dmsmccann/Spectrum-Analyzer/images/70mhz-lp-50mhz-to-100mhz.png

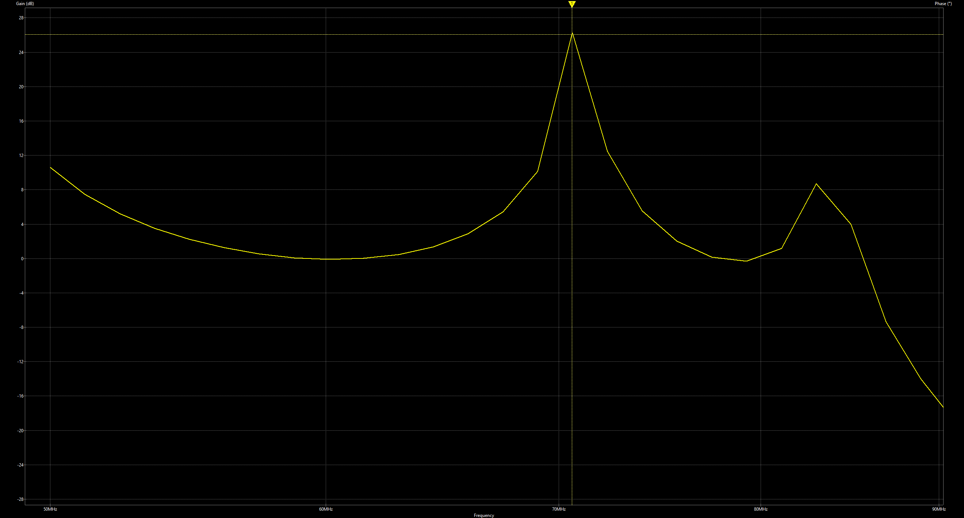
images/70mhz-lp-50mhz-to-100mhz.png
