dmsmccann/Spectrum-Analyzer/resolution-filters/resolution-filters/crystal-filter-nanovna-h4_2023-01-16_13-13-07.png

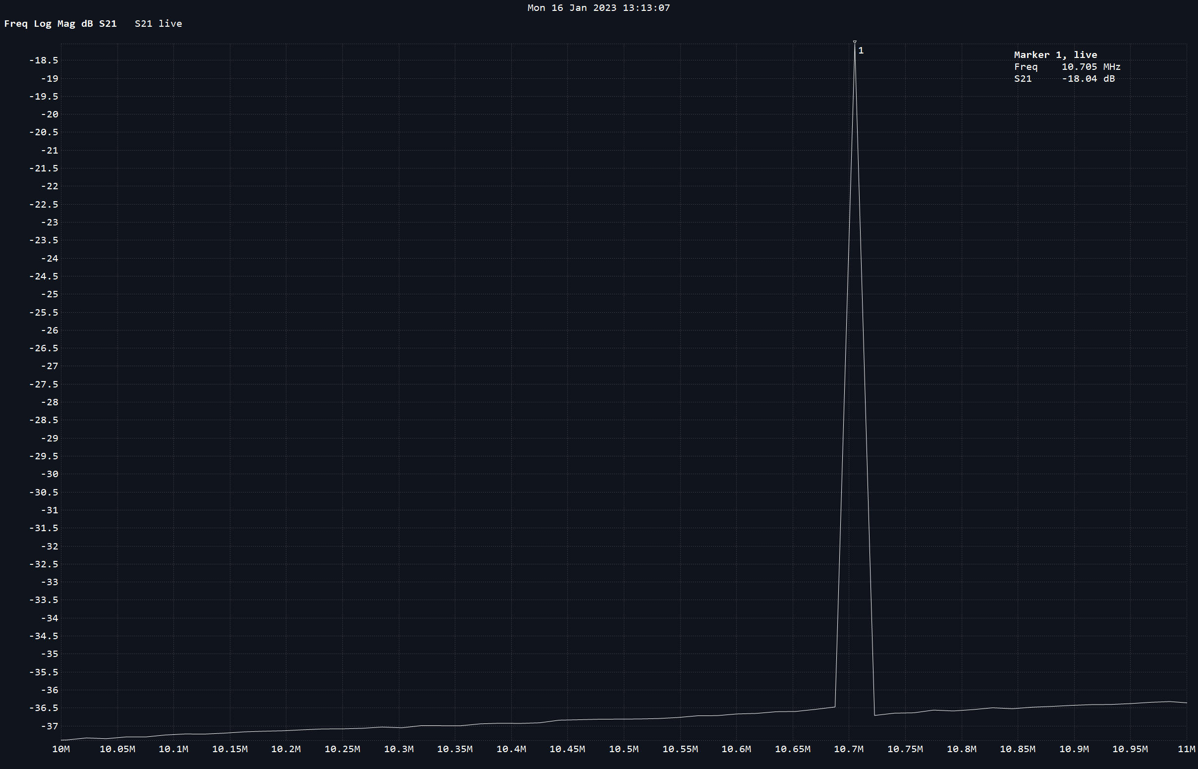
resolution-filters/resolution-filters/crystal-filter-nanovna-h4_2023-01-16_13-13-07.png
