dmsmccann/Spectrum-Analyzer/resolution-filters/resolution-filters/l501-smith-chart.png

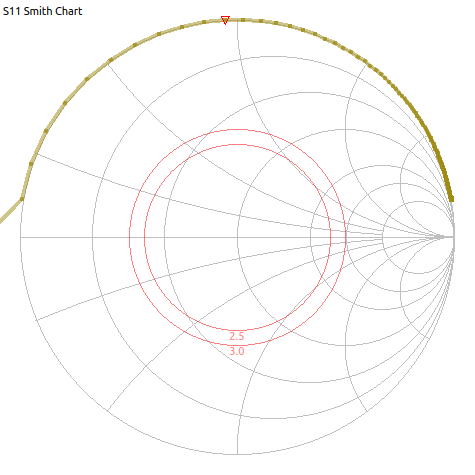
resolution-filters/resolution-filters/l501-smith-chart.png
