dmsmccann/Spectrum-Analyzer/Screenshot 2022-08-23 135709.gif

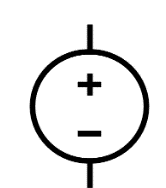
Screenshot 2022-08-23 135709.gif
