dmsmccann/Spectrum-Analyzer/tracking-generator/Screenshot 2023-12-05 054804.png

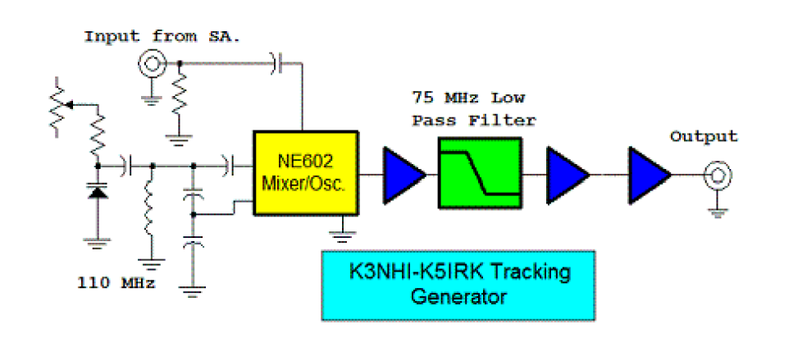
tracking-generator/Screenshot 2023-12-05 054804.png
