dmsmccann/Spectrum-Analyzer/if-and-log-amp/if-and-log-amp/if-log-amp-models/if-log-amp-3D/terminal-block.FCStd

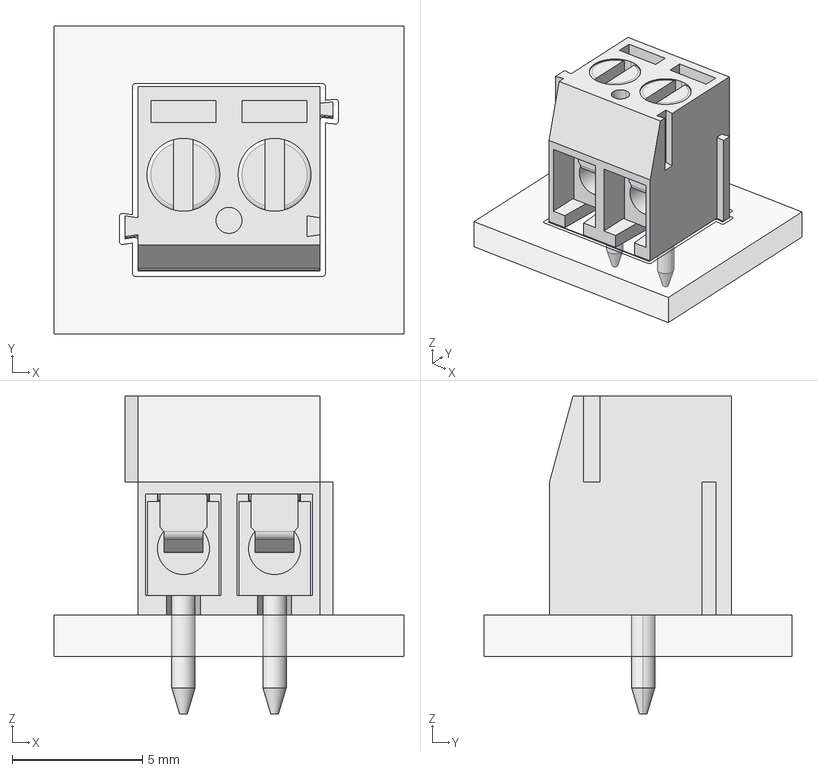
[picture p33: CAD file, 2022-08-05]
if-and-log-amp/if-and-log-amp/if-log-amp-models/if-log-amp-3D/terminal-block.FCStd
13.4 x 11.8 x 12.2 mm
FFab
FrontSilk
TopPads
BotPads
PTHs
Pcb
