dmsmccann/Spectrum-Analyzer/resolution-filters/resolution-filters/resolution-filters-models/resolution-filters-3D/UM-007.step

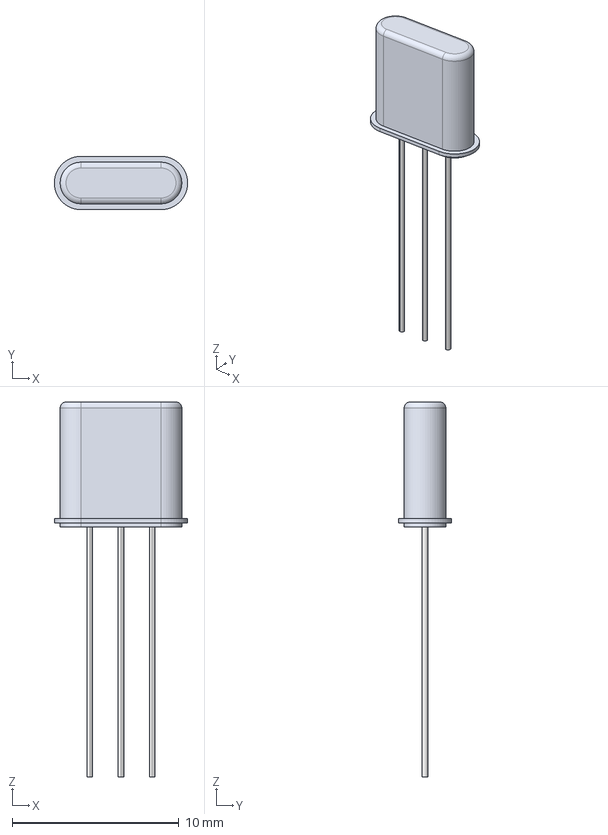
[picture p34: CAD file, 2022-08-05]
resolution-filters/resolution-filters/resolution-filters-models/resolution-filters-3D/UM-007.step
8.00 x 3.20 x 22.5 mm
UM-1
UM-002
UM-003
UM-004
UM-005
UM-006
