dmsmccann/Spectrum-Analyzer/15v-supply/15v-supply-models/15v-supply-3D/CAP_QYX_3P5X6X8P5_NCH.step

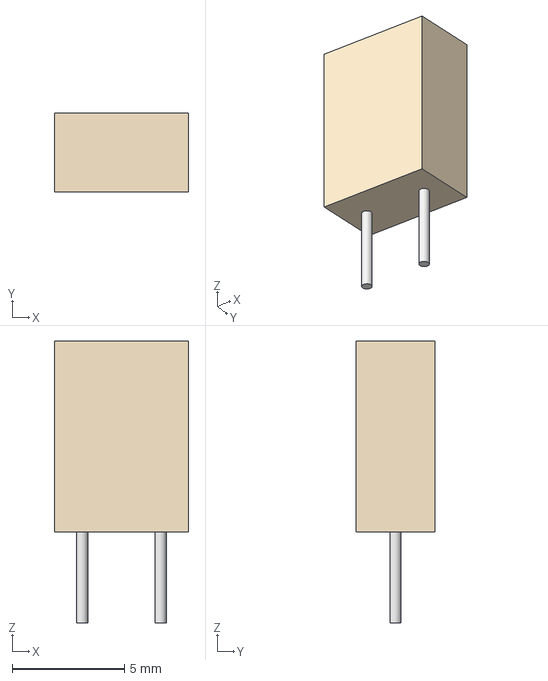
[picture p35: CAD file, 2022-06-16]
15v-supply/15v-supply-models/15v-supply-3D/CAP_QYX_3P5X6X8P5_NCH.step
5.99 x 3.51 x 12.6 mm
