dmsmccann/Spectrum-Analyzer/hierarchical-schematic/spectrum-analyzer-models/hammond-enclosure.FCStd

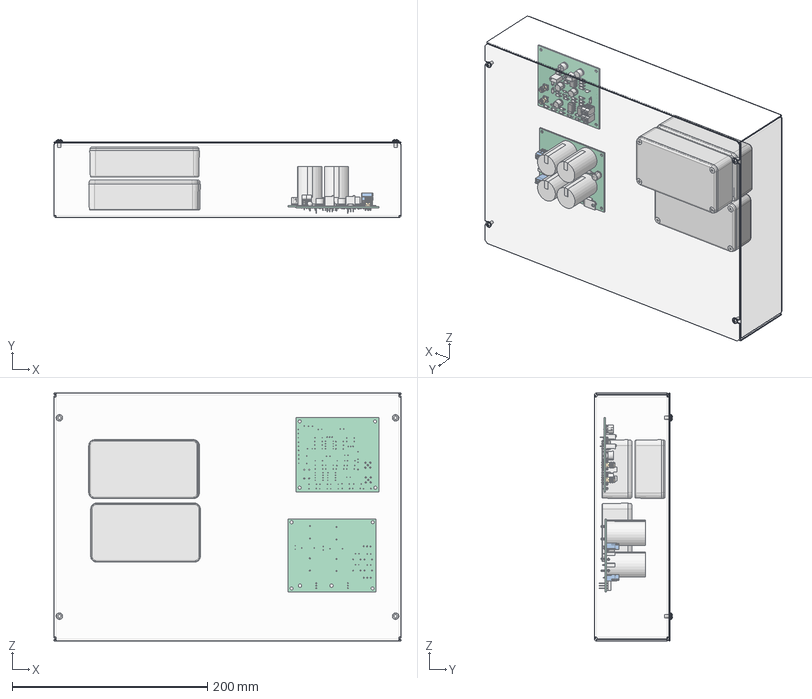
[picture p36: CAD file, 2023-04-26]
hierarchical-schematic/spectrum-analyzer-models/hammond-enclosure.FCStd
355.6 x 80.0 x 254.0 mm
1590B BOX
1590B-BS LID
SC530 (screw #6-32X 1_2' FH)
SC530 (screw #6-32X 1_2' FH)001
SC530 (screw #6-32X 1_2' FH)002
SC530 (screw #6-32X 1_2' FH)003
1590B BOX001
1590B-BS LID001
SC530 (screw #6-32X 1_2' FH)004
SC530 (screw #6-32X 1_2' FH)005
SC530 (screw #6-32X 1_2' FH)006
SC530 (screw #6-32X 1_2' FH)007
1590B BOX002
1590B-BS LID002
SC530 (screw #6-32X 1_2' FH)008
SC530 (screw #6-32X 1_2' FH)009
SC530 (screw #6-32X 1_2' FH)010
SC530 (screw #6-32X 1_2' FH)011
Pcb_7b02
D901_D_DO-41_SOD81_P7.62mm_Horizontal_0f7420698e15 x 4
R902_R_Axial_DIN0309_L90mm_D32mm_P1270mm_Horizontal_656395d6a1e4 x 2
C904_CP_Radial_D80mm_P350mm_be9362f17a2f x 2
U902_TO-220-3_Horizontal_TabUp_336c31f2f8c4 x 4
Pcb_758f
R426_R_Axial_DIN0207_L63mm_D25mm_P762mm_Horizontal_96b38c16849e x 27
D_DO-35_SOD27_P7.62mm_Horizontal x 7
D_DO-35_SOD27_P7.62mm_Horizontal001 x 7
C405_CP_Radial_D80mm_P350mm_98bf3544fc31 x 5
C401_C_Disc_D50mm_W25mm_P500mm_d1dd1edc5a97
OPA347PA x 3
OPA347PA001 x 3
OPA347PA002 x 3
OPA347PA003 x 3
OPA347PA004 x 3
OPA347PA005 x 3
OPA347PA006 x 3
OPA347PA007 x 3
OPA347PA008 x 3
OPA347PA009 x 3
R424_Potentiometer_Bourns_3296W_Vertical_5014a80db3f9 x 2
6-32 (SC18394)004
6-32 (SC18394)005
6-32 (SC18394)006
6-32 (SC18394)007
