dmsmccann/Spectrum-Analyzer/if-and-log-amp/if-and-log-amp/if-log-amp-models/if-log-amp-3D/ad8307.step

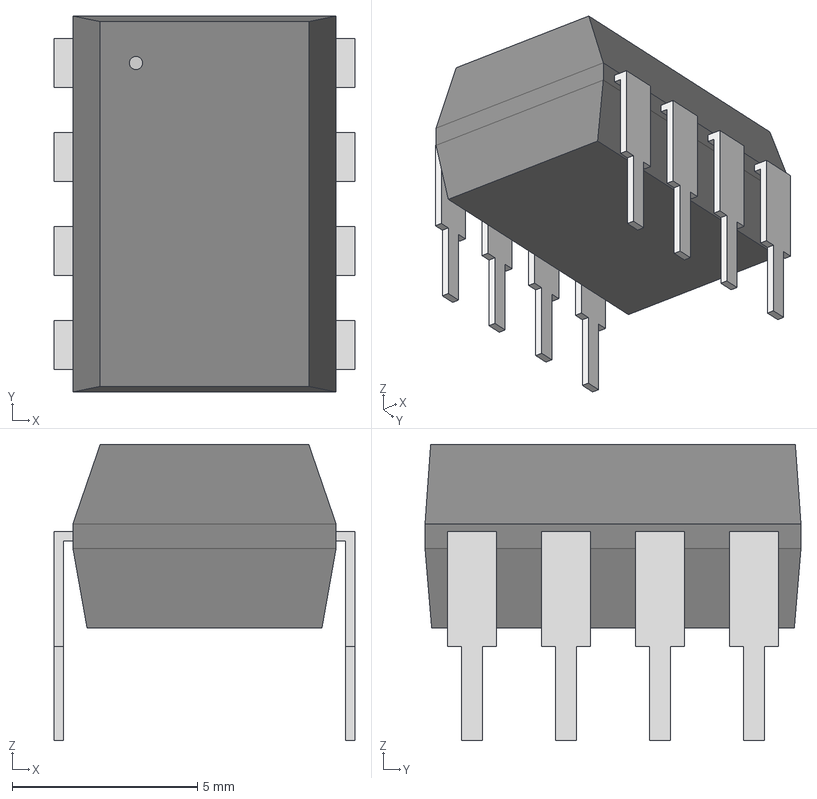
[picture p37: CAD file, 2022-08-05]
if-and-log-amp/if-and-log-amp/if-log-amp-models/if-log-amp-3D/ad8307.step
8.13 x 10.2 x 8.00 mm
