dmsmccann/Spectrum-Analyzer/15v-supply/15v-supply-models/15v-supply-3D/terminal-block-691103110003.step

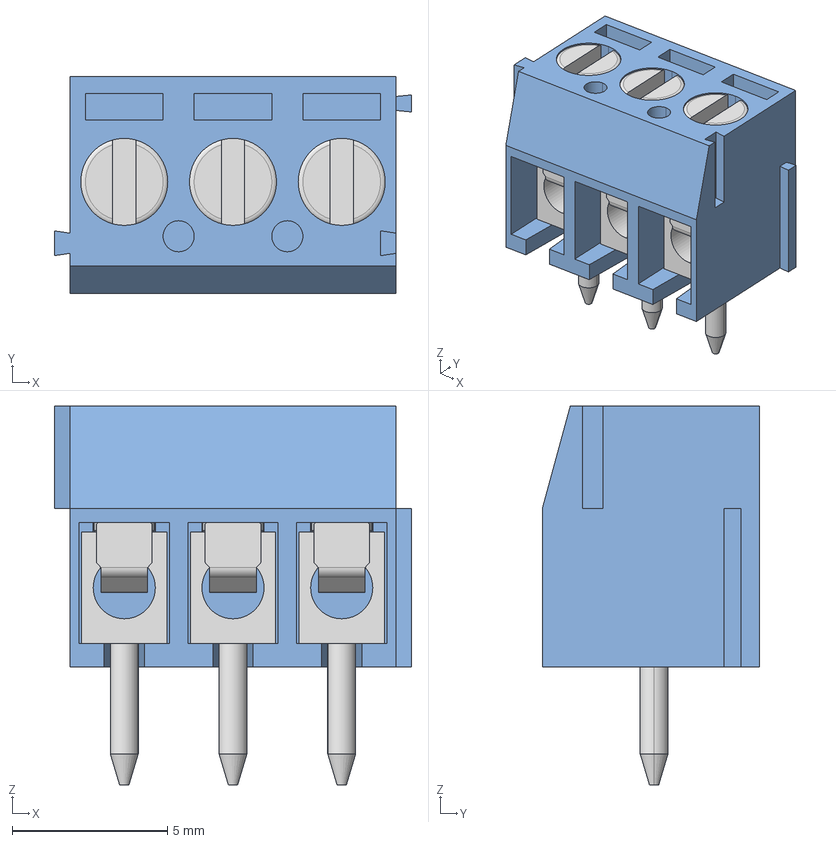
[picture p38: CAD file, 2022-06-16]
15v-supply/15v-supply-models/15v-supply-3D/terminal-block-691103110003.step
11.5 x 7.00 x 12.2 mm
