dmsmccann/Spectrum-Analyzer/hierarchical-schematic/spectrum-analyzer-models/1444-14103.stp

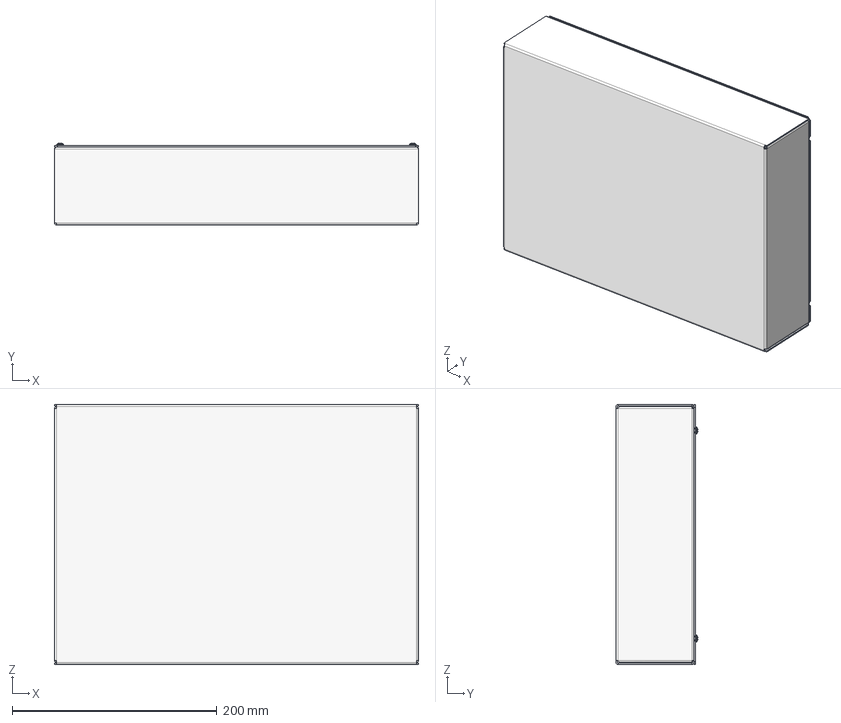
[picture p39: CAD file, 2023-04-26]
hierarchical-schematic/spectrum-analyzer-models/1444-14103.stp
355.6 x 80.0 x 254.0 mm
6-32 (SC18394) x 4
