dmsmccann/Spectrum-Analyzer/if-and-log-amp/if-and-log-amp/if-log-amp-models/if-log-amp-3D/toroid.FCStd

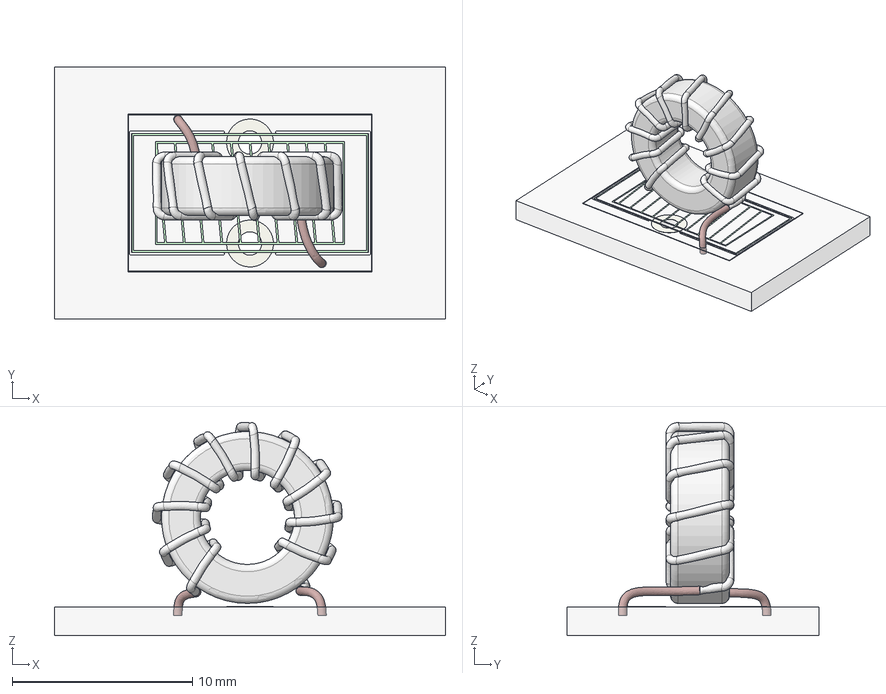
[picture p40: CAD file, 2022-08-05]
if-and-log-amp/if-and-log-amp/if-log-amp-models/if-log-amp-3D/toroid.FCStd
21.7 x 14.0 x 11.8 mm
FCrtYd
FFab
FrontSilk
TopPads
BotPads
PTHs
Pcb
T37-6 IND
T37-6 IND001
T37-6 IND002
T37-6 IND003
