dmsmccann/Spectrum-Analyzer/resolution-filters/resolution-filters/resolution-filters-models/resolution-filters-3D/T37-6 IND.STEP

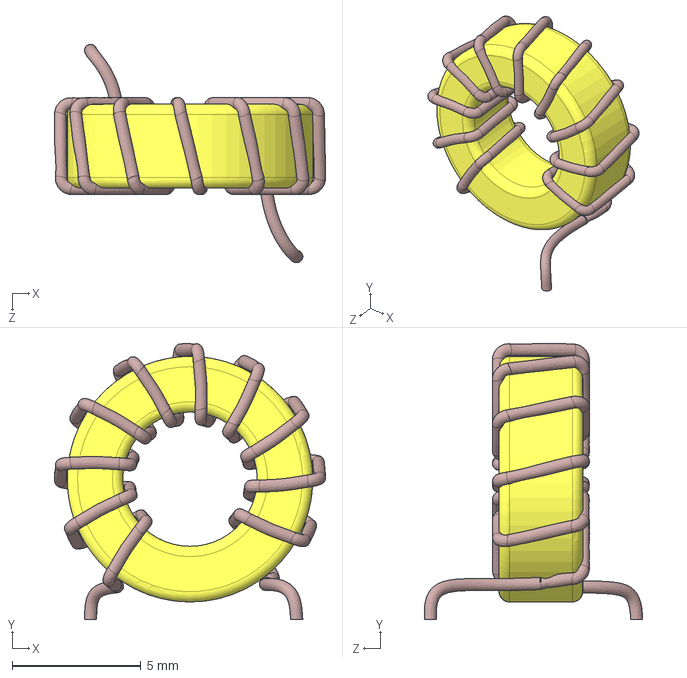
[picture p41: CAD file, 2022-08-05]
resolution-filters/resolution-filters/resolution-filters-models/resolution-filters-3D/T37-6 IND.STEP
10.5 x 10.7 x 8.47 mm
