dmsmccann/Spectrum-Analyzer/timebase/timebase/timebase-models/timebase-3D/NL17SZ74USG.step

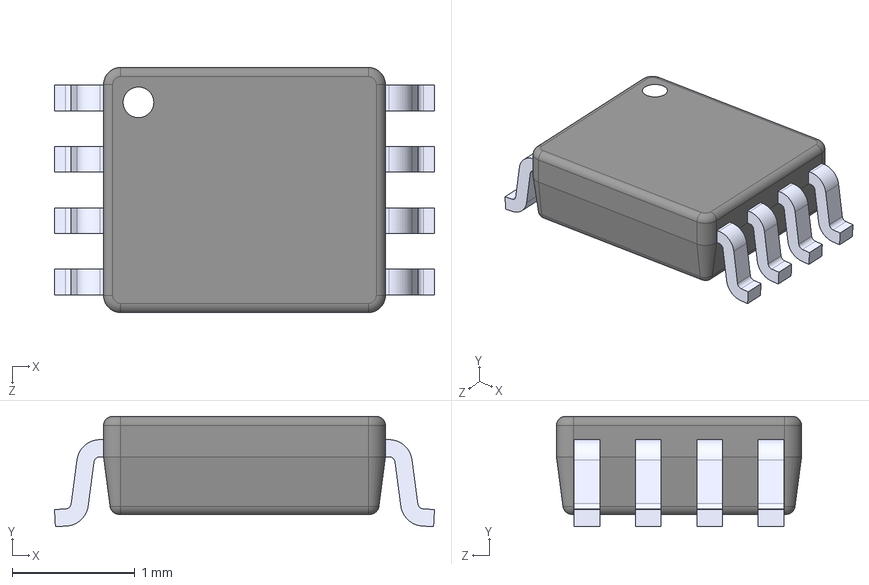
[picture p42: CAD file, 2022-06-18]
timebase/timebase/timebase-models/timebase-3D/NL17SZ74USG.step
3.10 x 0.9 x 2.00 mm
