dmsmccann/Spectrum-Analyzer/hierarchical-schematic/spectrum-analyzer-models/1590B.stp

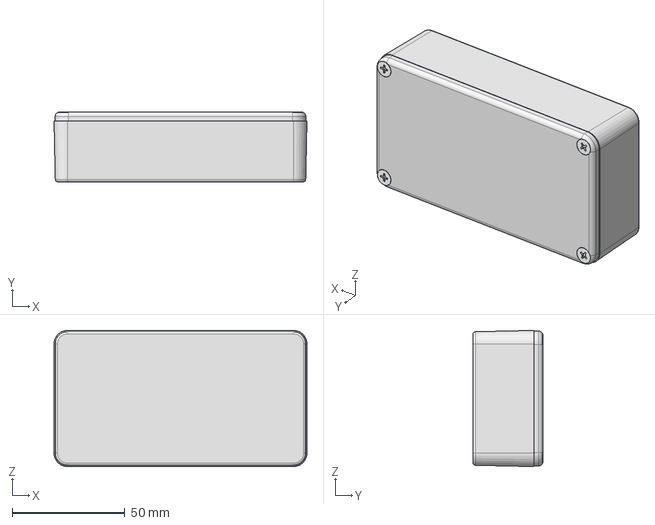
[picture p43: CAD file, 2022-06-01]
hierarchical-schematic/spectrum-analyzer-models/1590B.stp
112.4 x 31.0 x 60.5 mm
