dmsmccann/Spectrum-Analyzer/if-and-log-amp/if-and-log-amp/if-log-amp-models/if-log-amp-3D/Bourns 3386G.FCStd

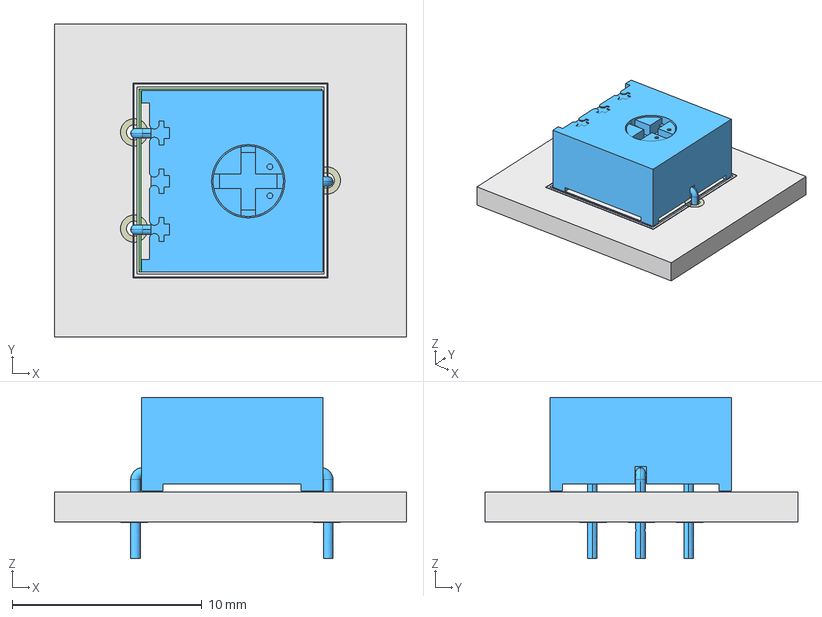
[picture p44: CAD file, 2022-08-05]
if-and-log-amp/if-and-log-amp/if-log-amp-models/if-log-amp-3D/Bourns 3386G.FCStd
18.6 x 16.5 x 8.51 mm
FCrtYd
FFab
FrontSilk
TopPads
BotPads
PTHs
Pcb
