dmsmccann/Spectrum-Analyzer/resolution-filters/resolution-filters/resolution-filters-models/resolution-filters-3D/L_Tor_13x8x5_3a.stp

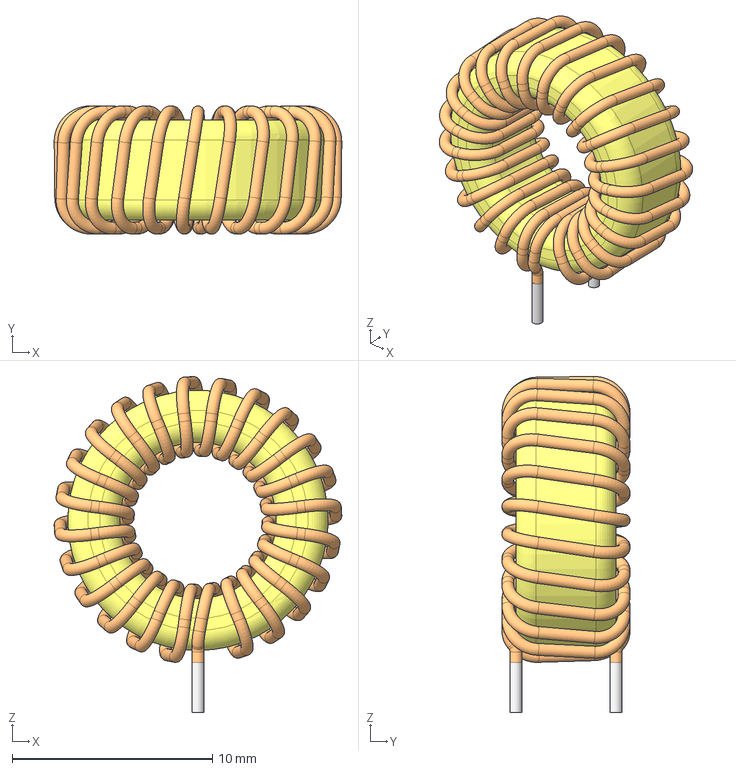
[picture p45: CAD file, 2022-08-05]
resolution-filters/resolution-filters/resolution-filters-models/resolution-filters-3D/L_Tor_13x8x5_3a.stp
14.4 x 6.40 x 16.8 mm
