dmsmccann/Spectrum-Analyzer/timebase/timebase/timebase-models/timebase-3D/CUI_Devices_PJ_009.step

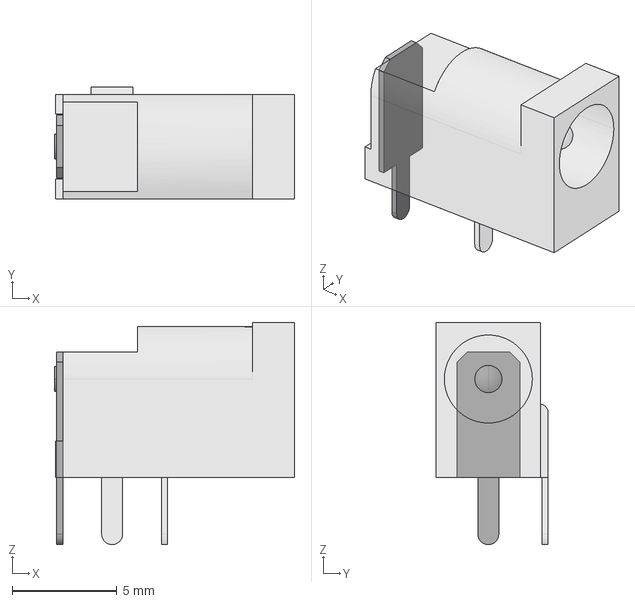
[picture p46: CAD file, 2022-06-18]
timebase/timebase/timebase-models/timebase-3D/CUI_Devices_PJ_009.step
11.5 x 5.35 x 10.6 mm
CUI_DEVICES_PJ-007
CUI_DEVICES_PJ-008
