dmsmccann/Spectrum-Analyzer/15v-supply/15v-supply-models/15v-supply-3D/terminal-block-on-footprint.FCStd

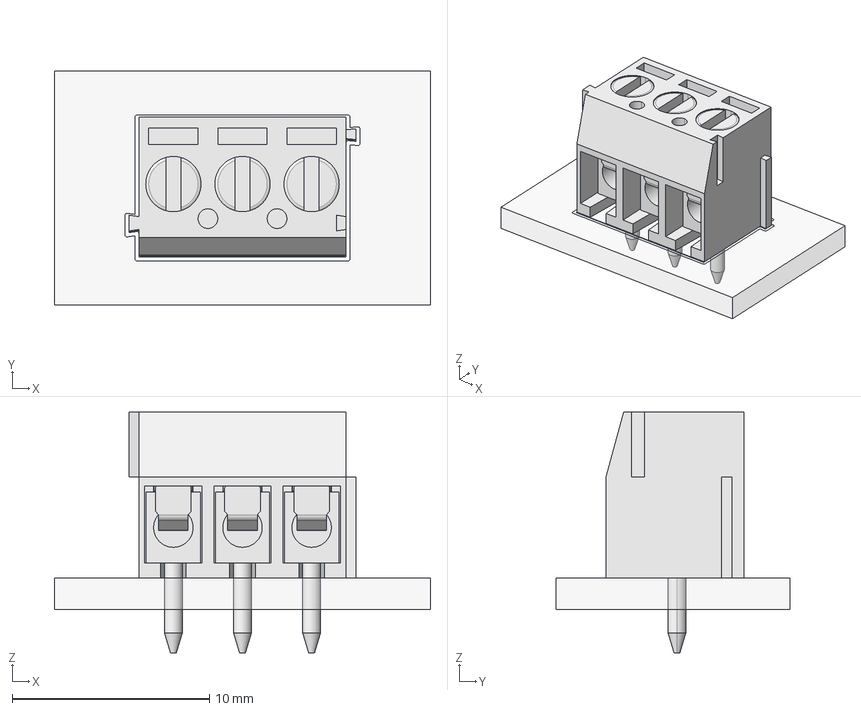
[picture p47: CAD file, 2022-06-16]
15v-supply/15v-supply-models/15v-supply-3D/terminal-block-on-footprint.FCStd
19.0 x 11.8 x 12.2 mm
FFab
FrontSilk
TopPads
BotPads
PTHs
Pcb
