dmsmccann/Spectrum-Analyzer/timebase/timebase/timebase-models/timebase-3D/LM358AP.step

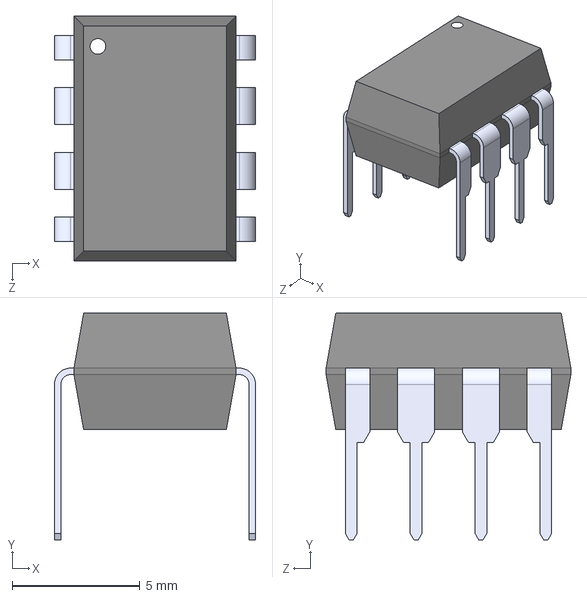
[picture p48: CAD file, 2022-06-18]
timebase/timebase/timebase-models/timebase-3D/LM358AP.step
7.87 x 8.89 x 9.59 mm
