dmsmccann/Spectrum-Analyzer/15v-supply/15v-supply-models/15v-supply-3D/panel switch.stp

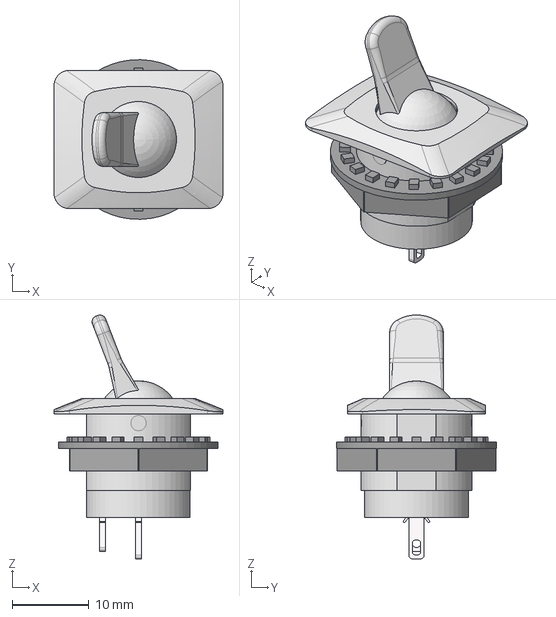
[picture p49: CAD file, 2022-06-15]
15v-supply/15v-supply-models/15v-supply-3D/panel switch.stp
22.0 x 20.8 x 31.8 mm
