dmsmccann/Spectrum-Analyzer/timebase/timebase/timebase-models/timebase-3D/5-1634503-1.step

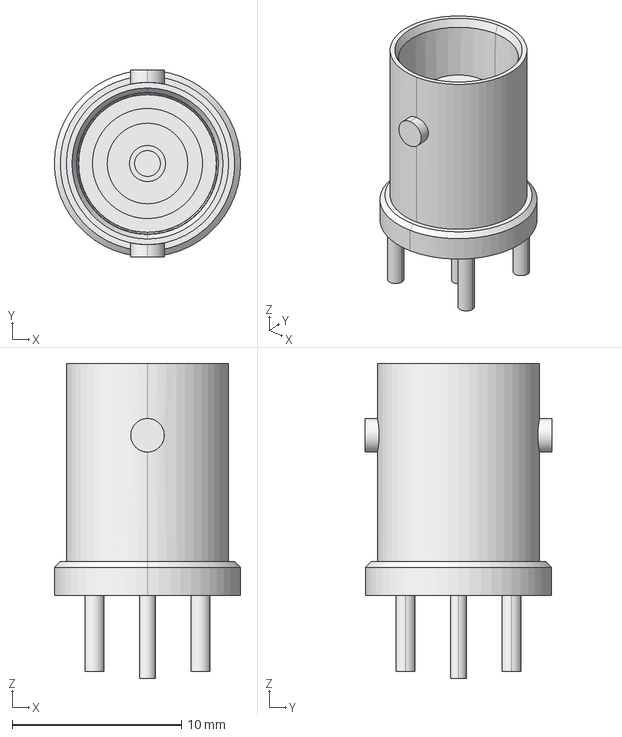
[picture p50: CAD file, 2022-06-18]
timebase/timebase/timebase-models/timebase-3D/5-1634503-1.step
11.0 x 11.0 x 18.6 mm
