dmsmccann/Spectrum-Analyzer/15v-supply/15v-supply-models/15v-supply-3D/fuse-holder.stp

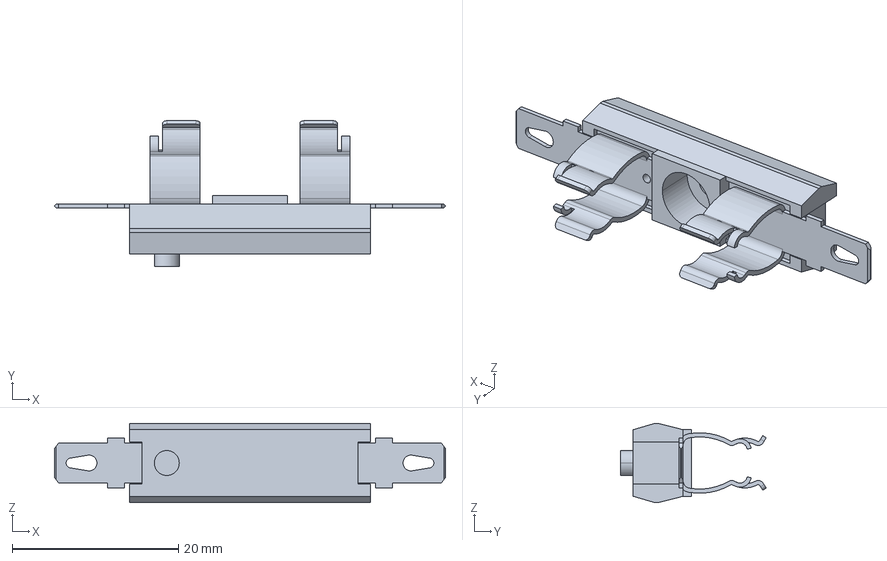
[picture p51: CAD file, 2022-06-15]
15v-supply/15v-supply-models/15v-supply-3D/fuse-holder.stp
47.0 x 17.5 x 9.50 mm
