dmsmccann/Spectrum-Analyzer/if-and-log-amp/if-and-log-amp/if-log-amp-models/if-log-amp-3D/if-and-log-amp-board.FCStd

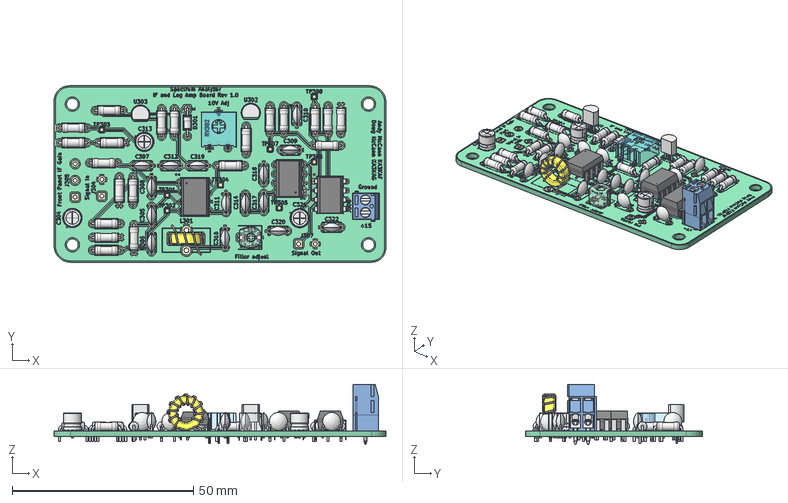
[picture p52: CAD file, 2022-08-05]
if-and-log-amp/if-and-log-amp/if-log-amp-models/if-log-amp-3D/if-and-log-amp-board.FCStd
91.7 x 48.8 x 16.6 mm
Pcb_cd3
topPads_cd3
topTracks_cd3
topZones_cd3
botPads_cd3
botTracks_cd3
botZones_cd3
topSilks_b243
R312_R_Axial_DIN0207_L63mm_D25mm_P762mm_Horizontal_d8800c764c18 x 21
T37-6 IND x 2
T37-6 IND001 x 2
T37-6 IND002 x 2
T37-6 IND003 x 2
C305_C_Disc_D50mm_W25mm_P500mm_af24686a53ab x 15
D_DO-35_SOD27_P7.62mm_Horizontal
D_DO-35_SOD27_P7.62mm_Horizontal001
C315_Trimmer Cap - Brown_147f20cc58c8 x 2
C304_CP_Radial_D50mm_P250mm_152b455e995b x 3
RV302_33756-68028_1ee07bcbfc79 x 2
U302_TO-92_Inline_Narrow_4b0f5a09eaed x 2
