dmsmccann/Spectrum-Analyzer/resolution-filters/resolution-filters/resolution-filters-models/resolution-filters-3D/transformer.FCStd

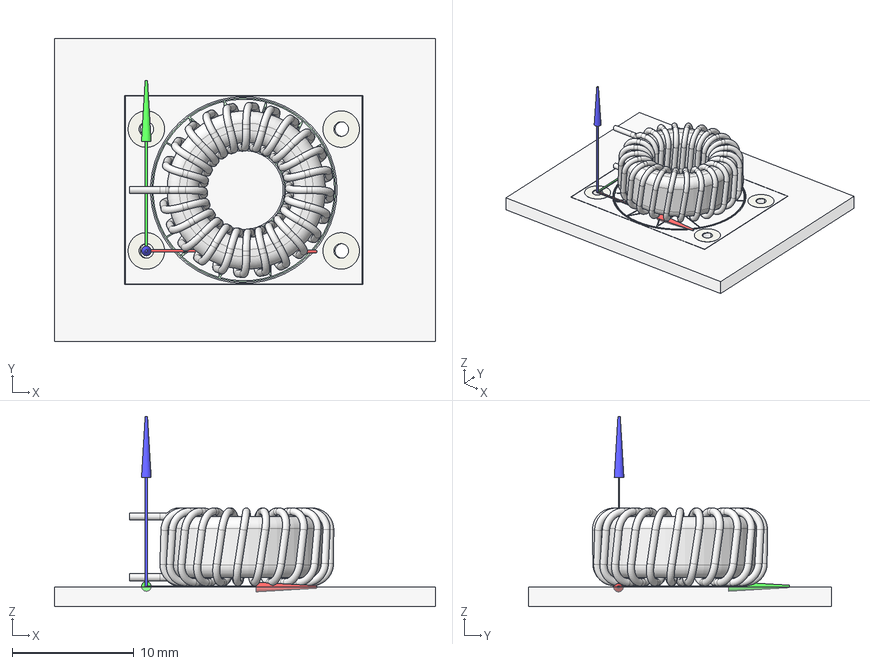
[picture p53: CAD file, 2022-08-05]
resolution-filters/resolution-filters/resolution-filters-models/resolution-filters-3D/transformer.FCStd
31.3 x 24.9 x 15.6 mm
FCrtYd
FFab
FrontSilk
TopPads
BotPads
PTHs
Pcb
Z
Y
X
L_Tor_13x8x5_3a_cp
