dmsmccann/Spectrum-Analyzer/timebase/timebase/timebase-models/timebase-3D/TE_5_1634503.FCStd

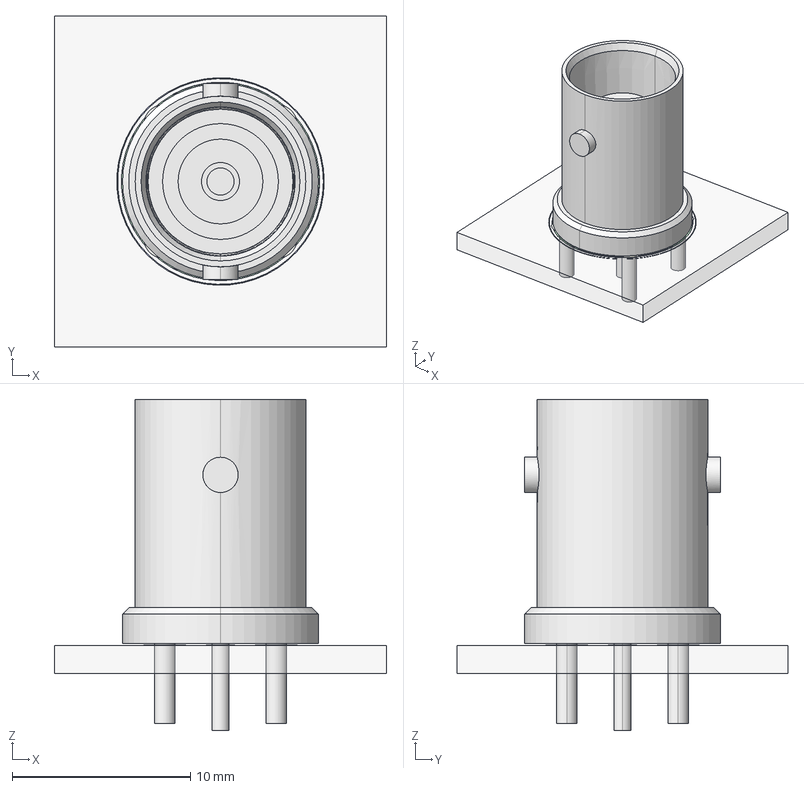
[picture p54: CAD file, 2022-06-18]
timebase/timebase/timebase-models/timebase-3D/TE_5_1634503.FCStd
18.6 x 18.6 x 18.6 mm
FCrtYd
FFab
FrontSilk
TopPads
BotPads
PTHs
Pcb
