dmsmccann/Spectrum-Analyzer/15v-supply/15v-supply-models/15v-supply-3D/6800u-U1-BBB_NCH.step

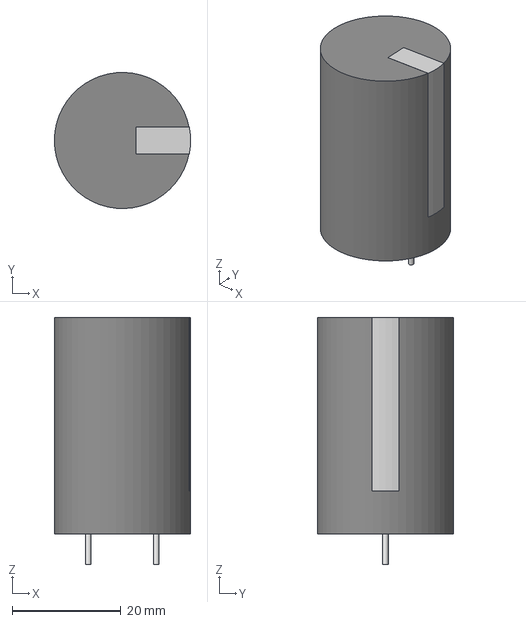
[picture p55: CAD file, 2022-06-15]
15v-supply/15v-supply-models/15v-supply-3D/6800u-U1-BBB_NCH.step
25.0 x 25.0 x 45.4 mm
