dmsmccann/Spectrum-Analyzer/timebase/timebase/timebase-models/timebase-3D/PRT-12748.step

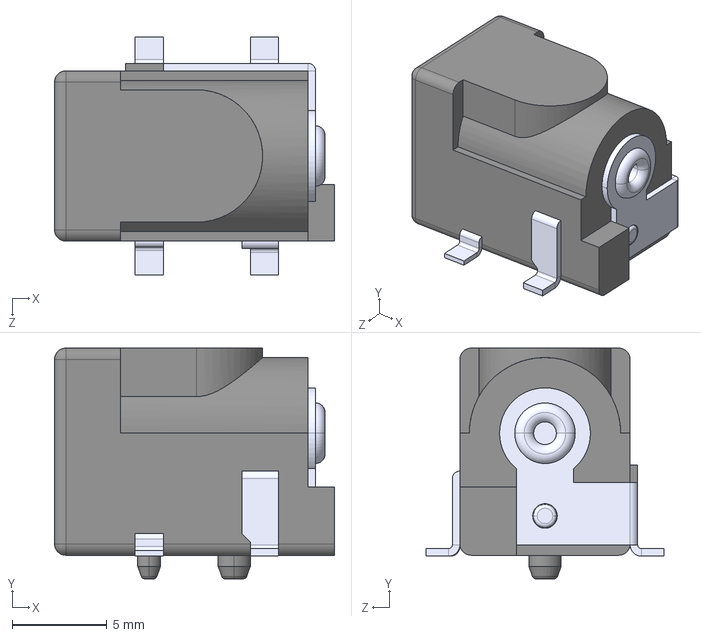
[picture p57: CAD file, 2022-06-18]
timebase/timebase/timebase-models/timebase-3D/PRT-12748.step
14.8 x 12.2 x 12.6 mm
