dmsmccann/Spectrum-Analyzer/15v-supply/15v-supply-models/15v-supply-3D/1N5060-SOD-57_BYT62-BY203.stp

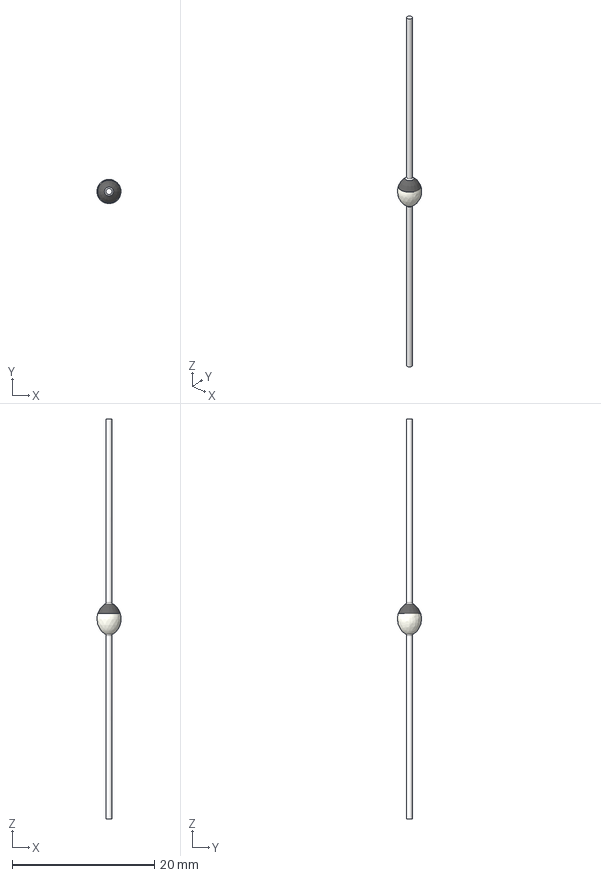
[picture p58: CAD file, 2022-06-15]
15v-supply/15v-supply-models/15v-supply-3D/1N5060-SOD-57_BYT62-BY203.stp
3.40 x 3.40 x 56.2 mm
