dmsmccann/Spectrum-Analyzer/timebase/timebase/timebase-models/timebase-3D/CUI-PJ-007.FCStd

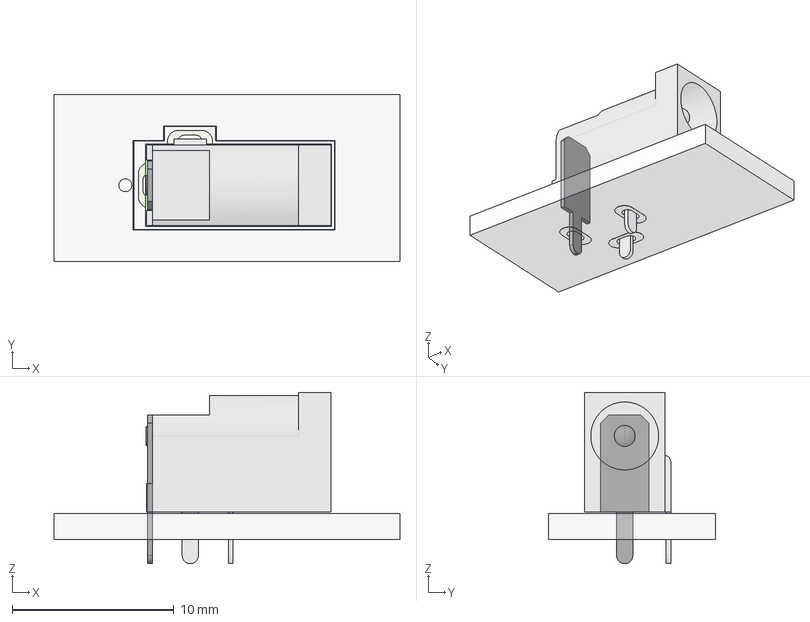
[picture p59: CAD file, 2022-05-30]
timebase/timebase/timebase-models/timebase-3D/CUI-PJ-007.FCStd
21.4 x 10.3 x 10.6 mm
FCrtYd
FFab
FrontSilk
TopPads
BotPads
PTHs
Pcb
CUI_DEVICES_PJ-007
CUI_DEVICES_PJ-008
