dmsmccann/Spectrum-Analyzer/15v-supply/15v-supply-models/15v-supply-3D/7915-TO220-3_ONS.step

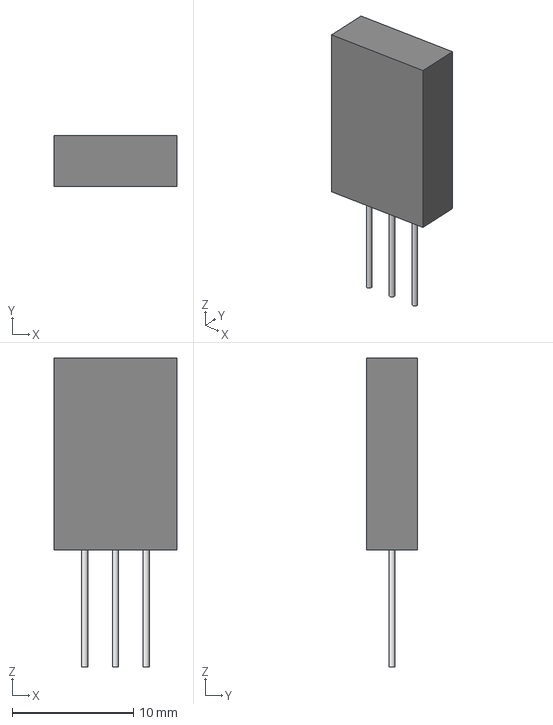
[picture p60: CAD file, 2022-06-15]
15v-supply/15v-supply-models/15v-supply-3D/7915-TO220-3_ONS.step
10.2 x 4.19 x 25.5 mm
