dmsmccann/Spectrum-Analyzer/if-and-log-amp/if-and-log-amp/if-log-amp-models/if-log-amp-3D/trimmer cap.FCStd

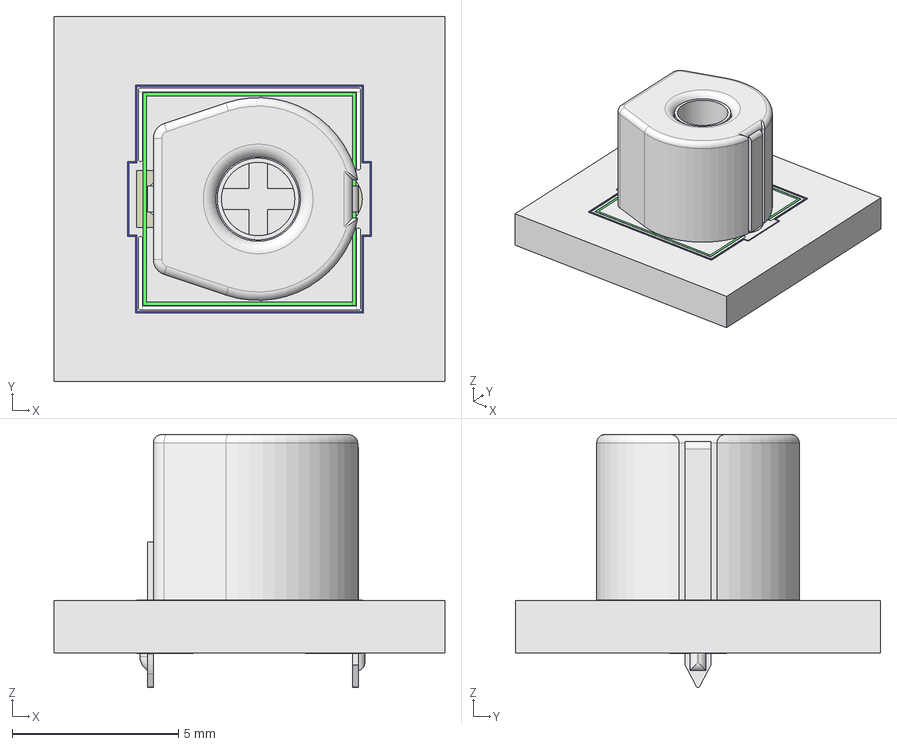
[picture p61: CAD file, 2022-08-05]
if-and-log-amp/if-and-log-amp/if-log-amp-models/if-log-amp-3D/trimmer cap.FCStd
11.7 x 11.0 x 7.61 mm
FCrtYd
FFab
FrontSilk
TopPads
BotPads
PTHs
Pcb
Trimmer Cap - Brown
