dmsmccann/Spectrum-Analyzer/timebase/timebase/timebase-models/timebase-3D/LM358.FCStd

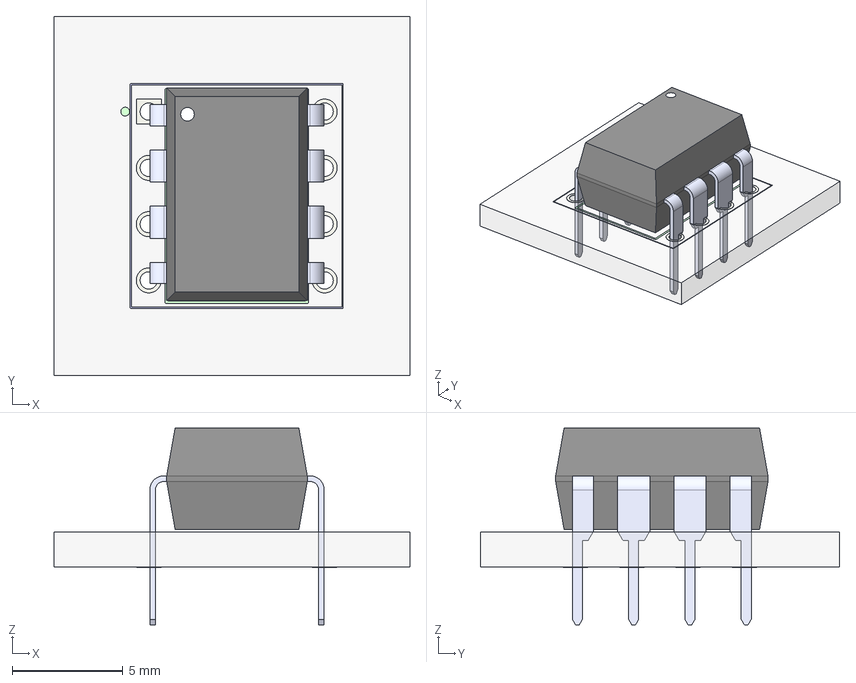
[picture p62: CAD file, 2022-05-30]
timebase/timebase/timebase-models/timebase-3D/LM358.FCStd
16.1 x 16.2 x 8.89 mm
FCrtYd
FFab
FrontSilk
TopPads
BotPads
PTHs
Pcb
OPA347PA
OPA347PA001
OPA347PA002
OPA347PA003
OPA347PA004
OPA347PA005
OPA347PA006
OPA347PA007
OPA347PA008
OPA347PA009
