dmsmccann/Spectrum-Analyzer/if-and-log-amp/if-and-log-amp/if-log-amp-models/if-log-amp-3D/Download_STP_691103110002 (rev1).stp

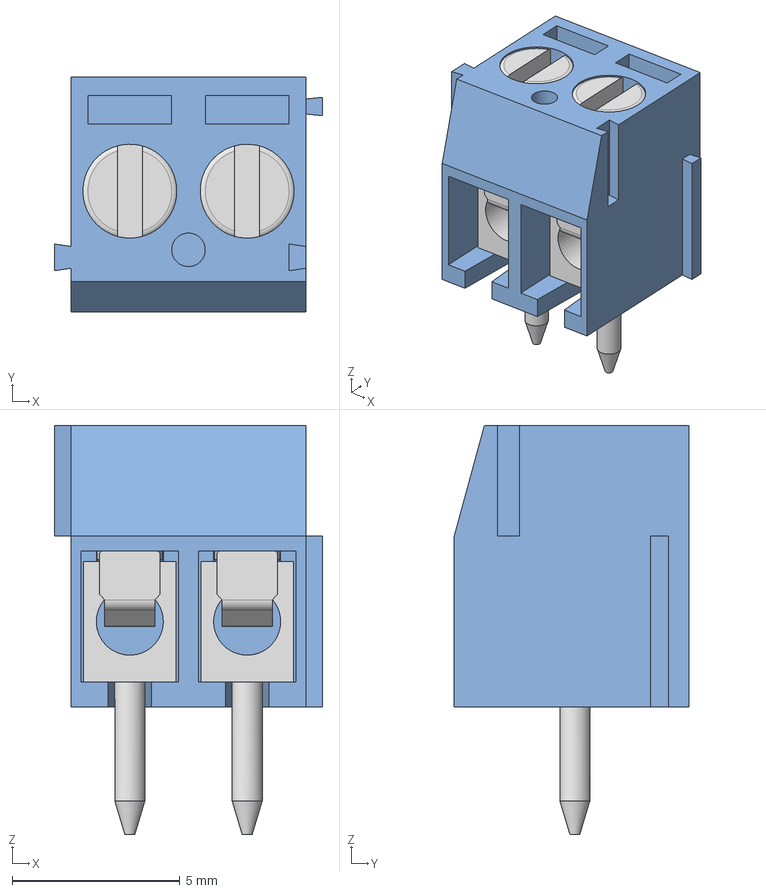
[picture p63: CAD file, 2022-08-05]
if-and-log-amp/if-and-log-amp/if-log-amp-models/if-log-amp-3D/Download_STP_691103110002 (rev1).stp
8.00 x 7.00 x 12.2 mm
6911031100xx_CAGE x 2
6911031100xx_PIN x 2
6911031100xx_VIS x 2
