dmsmccann/Spectrum-Analyzer/if-and-log-amp/if-and-log-amp/if-log-amp-models/if-log-amp-3D/DSS1NB32A102Q91A.stl

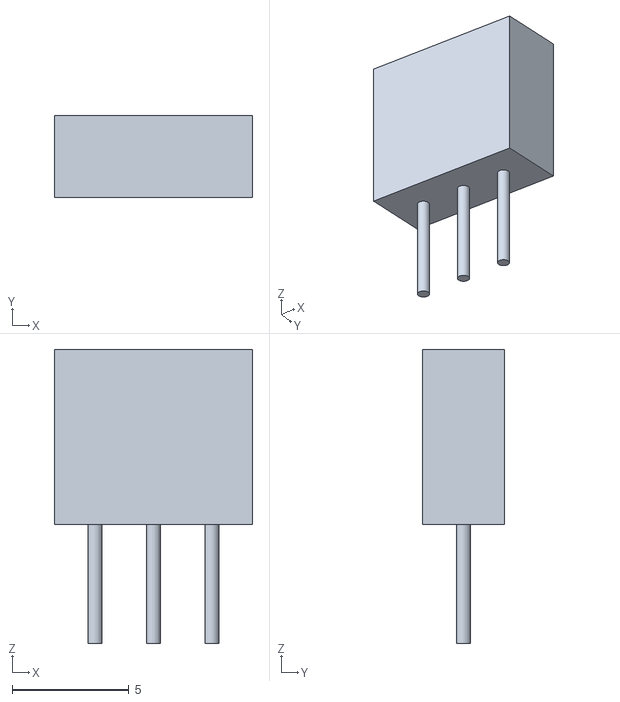
[picture p64: CAD file, 2022-07-20]
if-and-log-amp/if-and-log-amp/if-log-amp-models/if-log-amp-3D/DSS1NB32A102Q91A.stl
8.50 x 3.50 x 12.6
