dmsmccann/Spectrum-Analyzer/if-and-log-amp/if-and-log-amp/if-log-amp-models/if-log-amp-3D/TO-92_STM.step

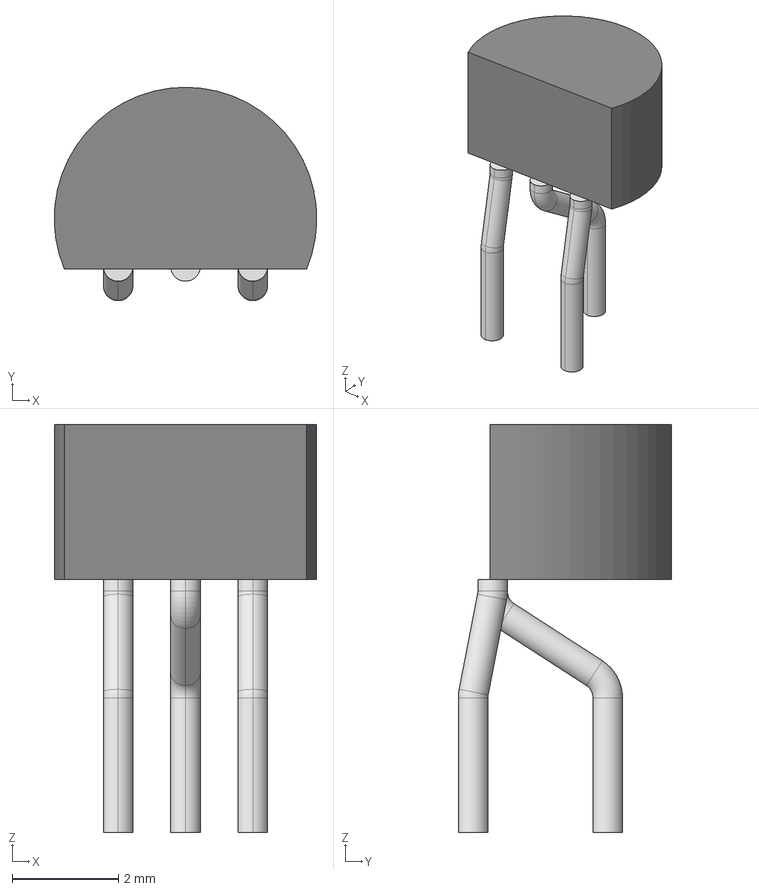
[picture p65: CAD file, 2022-06-15]
if-and-log-amp/if-and-log-amp/if-log-amp-models/if-log-amp-3D/TO-92_STM.step
4.95 x 4.03 x 7.70 mm
