dmsmccann/Spectrum-Analyzer/7mhz-crystal-oscillator/7mhz oscillator.asc

C1: cap; .1µ
C2: cap; .1µ
C3: cap; 470p
C4: cap; 470p
C5: xtal; 19.6f; Rser=972.5 Lser=26m Cpar=6.18p
Q1: npn; 2N3904
R1: res; 10k
R2: res; 51
R3: res; 100k
R4: res; 1k
R5: res; 100k
V1: voltage; 9; AC 1
Named nets: 0, Out
.ac dec 1Meg 6.5Meg 7.5Meg
.tran 0 10m 0 100n
