dmsmccann/Spectrum-Analyzer/70mhz-lpf/70mhz-lpf/70mhz-lpf.asc

C1: cap; 47p
C2: cap; 82p
C3: cap; 82p
C4: cap; 82p
C5: cap; 47p
L1: ind; 150n
L2: ind; 180n
L3: ind; 180n
L4: ind; 150n
R1: res; 50
V1: voltage; ""; AC 1
Named nets: 0
.ac dec 1001 1k 100meg
.net I(R1) V1
