dmsmccann/Spectrum-Analyzer/15v-supply/15v-supply-spice/15v-supply.asc

C1: cap; .01µ
C2: cap; .01µ
C3: cap; .01µ
C4: cap; .01µ
C5: polcap; 6800µ
C6: polcap; 6800µ
C7: polcap; 6800µ
C8: polcap; 6800µ
C9: cap; 6.8µ
C10: cap; 6.8µ
C11: cap; .22µ
D1: diode; 1N5060
D2: diode; 1N5060
D3: diode; 1N5060
D4: diode; 1N5060
L1: ind2; 1600µ
L2: ind2; 100µ
L3: ind2; 100µ
R1: res; 2.2k
R2: res; 2.2k
U1: LM7815
U2: LM7915
V1: voltage; SINE(0 120 60); Rser=.1
Named nets: 0
.lib 1n5060.lib
.tran 200m
.lib regulators.lib
K1 L1 L2 L3 .999
