dmsmccann/Spectrum-Analyzer/vco-1stmixer/vco-1stmixer/vco-1stmixer-spice/mixer.asc

D1: diode
D2: diode
D3: diode
D4: diode
L1: ind2; 1µ; Rser=50
L2: ind2; .5µ
L3: ind2; .5µ
L4: ind2; .5µ
L5: ind2; .5µ
L6: ind2; 1µ; Rser=50
V1: voltage; SINE(0 1 700)
V2: voltage; SINE(0 1 1900)
Named nets: 0, R, I, L
K L1 L2 L3 1
K2 L4 L5 L6 1
.tran 10m
