dmsmccann/Spectrum-Analyzer/2ndmixer-2ndlo/2ndmixer-2ndlo/2ndmixer-2ndlo-spice/diplexer.asc

C1: cap; 120p
C2: cap; .1µ
C3: cap; .1µ
D1: diode
D2: diode
D3: diode
D4: diode
L1: ind2; 10µ
L2: ind2; 10µ
L3: ind2; 10µ
L4: ind2; 10µ
L5: ind2; 10µ
L6: ind2; 10µ
L7: ind2; 1µ
L8: ind2; 10µ
L9: ind2; 10µ
L10: ind2; 10µ
Q1: npn; 2N5179
R1: res; 51
R2: res; 50
R3: res; 50
R4: res; 50
R5: res; 27
R6: res; 5.1
R7: res; 2k
R8: res; 390
R9: res; 27
R10: res; 50
V1: voltage; +15
VLO: voltage; SINE(0 6.3 100Meg); AC 1
Vrf: voltage; SINE(0 .3 10Meg); AC 1
Named nets: 0, Out, I, +15
.tran 0 500nn 0 10n
K1 L1 L2 L3 1
K2 L4 L5 L6 1
K3 L8 L9 L10 1
.ac dec 1000 100k 150Meg
.include C:\\Users\\Dougl\\OneDrive\\Ham Radio\\KiCad Files\\KiCad-Spice-Library-master\\Models\\Transistor\\BJT\\bjt.lib
