dmsmccann/Spectrum-Analyzer/2ndmixer-2ndlo/2ndmixer-2ndlo/2nd-lo-kanga/kanga-lo.asc

C1: cap; 470p
C2: cap; 470p
C3: cap; 33p
C4: cap; 33p
C5: cap; 12p
C6: cap; 15p
C7: cap; 82p
L1: ind; 65n
L2: ind; 420n
Q1: npn
R1: res; 3.3k
R2: res; 39
R3: res; 2k
R4: res; 100
R5: res; 510
R6: res; 100
V1: voltage; 15
Named nets: 0, +15
.tran 0 10u 0 10n
