dmsmccann/Spectrum-Analyzer/2ndmixer-2ndlo/2ndmixer-2ndlo/2ndmixer-2ndlo-spice/2nd-lo.asc

C201: cap; 470p
C203: cap; 470p
C204: cap; 33p
C205: cap; 33p
C206: cap; 5p
C207: cap; 15p
C208: cap; 82p
L201: ind; 40n
Q201: npn; 2N5179
R1: res; 100
R201: res; 3.3k
R202: res; 39
R203: res; 2k
R204: res; 100
R205: res; 510
R206: res; 150
R207: res; 36
R208: res; 150
V1: voltage; 15
Named nets: 0, +15, Out1, Out2
.tran 0 500n 0
.lib "C:\\Users\\Dougl\\OneDrive\\Ham Radio\\KiCad Files\\W7ZOI Spectrum Analyzer\\2ndmixer-2ndlo\\2ndmixer-2ndlo\\2ndmixer-2ndlo-spice\\2N5179.LIB"
