dmsmccann/Spectrum-Analyzer/resolution-filters/resolution-filters/resolution-filters-spice/Draft1.asc

C1: cap; 22p
R1: res; 1k
V1: voltage; ""; AC 1 0; Rser=50
Named nets: 0
.ac dec 1000 1khz 200Meg
;net I (R7) V1
