dmsmccann/Spectrum-Analyzer/resolution-filters/resolution-filters/resolution-filters-spice/staged-300khz-bandwith-10mhz-lc-filter.asc

C1: cap; 56p
C2: cap; 120p
C3: cap; 30p
C4: cap; 100p
C5: cap; 5.6p
C6: cap; 30p
C7: cap; 150p
C8: cap; 3.3p
C9: cap; 30p
C10: cap; 150p
C11: cap; 5.6p
C12: cap; 30p
C13: cap; 100p
C14: cap; 56p
C15: cap; 120p
L1: ind; 1.15µ
L2: ind; 1.15µ
L3: ind; 1.3µ
L4: ind; 1.3µ
R1: res; 36
R2: res; 150
R3: res; 150
R4: res; 10Meg
R5: res; 10Meg
R6: res; 0
R7: res; 50
U1: spdt
V1: voltage; ""; AC 1 0; Rser=50
Named nets: In, 0, Out
.ac dec 1000 1khz 200Meg
.net I (R7) V1
.subckt SPDT COM NO NC POS NEG
S1 COM NO POS NEG MYSW1
S2 COM NC NEG POS MYSW2
.model MYSW1 SW(Ron=.01 Roff=1000Meg Vh=.25 Vt=.5)
.model MYSW2 SW(Ron=.01 Roff=1000Meg Vh=.25 Vt=-.5)
.ends
