dmsmccann/Spectrum-Analyzer/resolution-filters/resolution-filters/resolution-filters-spice/300khz bandwith 10mhz LC filter.asc

C1: cap; 56p
C2: cap; 120p
C3: cap; 60p
C4: cap; 100p
C5: cap; 5.6p
C6: cap; 60p
C7: cap; 150p
C8: cap; 3.3p
C9: cap; 60p
C10: cap; 150p
C11: cap; 5.6p
C12: cap; 60p
C13: cap; 100p
C14: cap; 56p
C15: cap; 120p
L1: ind; 1.15µ
L2: ind; 1.15µ
L3: ind; 1.15µ
L4: ind; 1.15µ
R1: res; 36
R2: res; 150
R3: res; 150
R4: res; 10Meg
R5: res; 10Meg
R6: res; 0
R7: res; 50
V1: voltage; ""; AC 1 0; Rser=50
Named nets: In, 0, Out, Pad2
.ac dec 1000 1khz 200Meg
.net I (R7) V1
