dmsmccann/Spectrum-Analyzer/if-and-log-amp/if-and-log-amp/if-log-amp-spice/IF and Log Amplifier-as-built.asc

C1: cap; .01µ
C2: cap; .1µ
C3: polcap; 100µ
C4: cap; .1µ
C5: cap; 18µ
C6: cap; .1µ
C7: cap; 5.6p
C8: cap; 5.6p
C9: cap; 60p
C10: cap; 200p
C11: cap; .1µ
C12: cap; .1µ
C13: cap; .001µ
C14: cap; .1µ
L1: ind; 1.01µ
R1: res; 100
R2: res; 51
R3: res; 2.2k
R4: res; 2.2k
R5: res; 10
R6: res; 4.3k
R7: res; 5.6k
R8: res; 1k
R9: res; 510
R10: res; 680
R11: res; 1k
R12: res; 10
R13: res; 680
R14: res; 1k
R15: res; 2.2k
R16: res; 51
U1: AD603
U2: potentiometer_standard
U3: AD8310
U5: UniversalOpAmp
V1: voltage; 10
V2: voltage; SINE(0 20m 10.7M)
V3: voltage; 5
V4: voltage; 15
Named nets: 0, Coax, +10, Out, +5, +15
5n FT capacitors on each pot pin
.tran 90
.ac list 10.7Meg
.step param C 140p 160p 1p
Simulation currently set up to do an AC analysis - frequency of interest is fixed at 10.7Meg using ac list statement
then capacitor value "C" stepped from 140p to 160p at 1p intervals to determine best value
