dmsmccann/Spectrum-Analyzer/timebase/timebase/timebase-spice/TimeBase.asc

C401: cap; 1µ
C402: polcap; 22µ
C403: polcap; 22µ
C404: polcap; 100µ
C405: polcap; 100µ
C406: polcap; 100µ
D401: diode; 1N4148
D402: diode; 1N4148
D403: zener
D404: diode; 1N4148
D405: diode; 1N4148
D406: zener
D407: diode; 1N4148
D408: diode; 1N4148
R4: potentiometer_standard
R5: potentiometer_standard; Rtot=5K wiper=.5
R6: potentiometer_standard
R16: res; 680k
R401: res; 56k
R403: res; 100
R404: res; 100
R405: res; 2.2k
R406: res; 2.2k
R407: res; 4.7k
R409: res; 2.2k
R410: res; 2.2k
R411: res; 12k
R412: res; 15k
R413: res; 10k
R414: res; 10k
R415: res; 15k
R416: res; 390
R417: res; 51
R418: res; 10k
R419: res; 10k
R420: potentiometer_standard
R421: res; 6.8k
R422: res; 240k
R423: res; 10k
R424: potentiometer_standard; Rtot=5K wiper=.5
R425: res; 10k
R426: res; 15k
R427: res; 22
R428: res; 22
R429: res; 470
U4: potentiometer_standard
U5: AD712
U6: AD712
U7: AD712
U8: AD712
U403A: AD712
U403B: AD712
V1: voltage; 15
V2: voltage; -15
Named nets: 0, V+15, V-15, Out, VCO_Out
.options gmin=1e-10
.options abstol=1e-10
;tran 0 500m 0 10m
.save V(out) dialogbox
;op
.op 0 800u 300u
