dmsmccann/Spectrum-Analyzer/if-and-log-amp/if-and-log-amp/if-log-amp-spice/10mhz-filter.asc

C1: cap; 5.6p
C2: cap; 5.6p
C3: cap; {C}
L1: ind; 1.05µ
R1: res; 1k
R2: res; 50
V1: voltage; SINE(0 1 10.7Meg); AC 1
Named nets: 0
.ac list 10.7Meg
.step param C 195p 205p .1p
