dmsmccann/Spectrum-Analyzer/if-and-log-amp/if-and-log-amp/if-log-amp-spice/AD8310.asc

C1: cap; 10n
C2: cap; 10n
C3: cap; 10p
C4: cap; 10p
R4: res; 52.3
R5: res; 1k
R6: res; 1k
U1: AD8310
V1: voltage; SINE(0 {2*pow(10,dBV/20)} {fin})
V3: voltage; 5
V4: voltage; 5
Named nets: vOUT, 0, INHI, INLO
.tran 400n
RF Signal Generator
.param fin=1e8
.param dBV 10
