dmsmccann/Spectrum-Analyzer/timebase/timebase/timebase-spice/TimeBase_top_half.asc

C401: cap; 1µ
C402: polcap; 22µ
C403: polcap; 22µ
D401: diode; 1N4148
D402: diode; 1N4148
D403: zener
D404: diode; 1N4148
D405: diode; 1N4148
D406: zener
R16: res; 680k
R401: res; 56k
R403: res; 100
R404: res; 100
R405: res; 2.2k
R406: res; 2.2k
R407: res; 4.7k
R408: res; 1k
R409: res; 2.2k
R410: res; 2.2k
R411: res; 12k
R412: res; 15k
R413: res; 10k
R414: res; 10k
R415: res; 15k
R416: res; 390
U1: potentiometer_standard; Rtot=10K wiper=.9
U2: AD712
U6: AD712
U7: AD712
U8: AD712
V1: voltage; 15
V2: voltage; -15
Named nets: 0, V+15, V-15, Out
;op
.tran 0 1 0 1m
